pablomaki/esp32-metronome/software/main/src/resources.c

#include "resources.h"

uint16_t signature_modes[SIGNATURE_IMAGES] = {4, 3, 2};
uint8_t segment_display_signatures[SIGNATURE_IMAGES][192] = {
    {//.... https://....www.iconspng.com/image/5656/seven-segment-display-gray-0
     //.... 'seven-segment-display-gray-0', 32x48px
     0x00, 0x00, 0x00, 0x00,
     0x00, 0x00, 0x00, 0x00,
     0x03, 0xc3, 0xc0, 0x00, //......XXXX....XXXX..............
     0x03, 0xc3, 0xc0, 0x00, //......XXXX....XXXX..............
     0x03, 0xc3, 0xc0, 0x00, //......XXXX....XXXX..............
     0x03, 0xc3, 0xc0, 0x00, //......XXXX....XXXX..............
     0x03, 0xc3, 0xc0, 0x00, //......XXXX....XXXX..............
     0x03, 0xc3, 0xc0, 0x00, //......XXXX....XXXX..............
     0x00, 0xff, 0xc0, 0x00, //........XXXXXXXXXX..............
     0x00, 0xff, 0xc0, 0x00, //........XXXXXXXXXX..............
     0x00, 0x03, 0xc0, 0x00, //..............XXXX..............
     0x00, 0x03, 0xc0, 0x00, //..............XXXX..............
     0x00, 0x03, 0xc0, 0x00, //..............XXXX..............
     0x00, 0x03, 0xc0, 0x00, //..............XXXX..............
     0x00, 0x00, 0x00, 0x00,
     0x00, 0x00, 0x00, 0x00,
     0x00, 0x00, 0x00, 0x00,
     0x00, 0x00, 0x00, 0x00,
     0x03, 0xc3, 0xc0, 0x00, //......XXXX....XXXX..............
     0x03, 0xc3, 0xc0, 0x00, //......XXXX....XXXX..............
     0x03, 0xc3, 0xc0, 0x00, //......XXXX....XXXX..............
     0x03, 0xc3, 0xc0, 0x00, //......XXXX....XXXX..............
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
        0x00, 0x00, 0x00, 0x00, //................................
        0x00, 0x00, 0x00, 0x00, //................................
        0x00, 0x00, 0x00, 0x00, //................................
        0x00, 0x00, 0x00, 0x00, //................................
        0x00, 0x00, 0x00, 0x00, //................................
        0x00, 0x00, 0x00, 0x00, //................................
        0x00, 0x00, 0x00, 0x00, //................................
        0x00, 0x00, 0x00, 0x00, //................................
        0x00, 0x00, 0x00, 0x00, //................................
        0x00, 0x00, 0x00, 0x00, //................................
        0x00, 0x00, 0x00, 0x00, //................................
        0x00, 0x00, 0x00, 0x00, //................................
        0x00, 0x00, 0x00, 0x00, //................................
        0x00, 0x00, 0x00, 0x00, //................................
        0x00, 0x00, 0x00, 0x00, //................................//
    },
};
